ImSota/ZaruBall_casedata/case/Right/bottom_noMack.stl

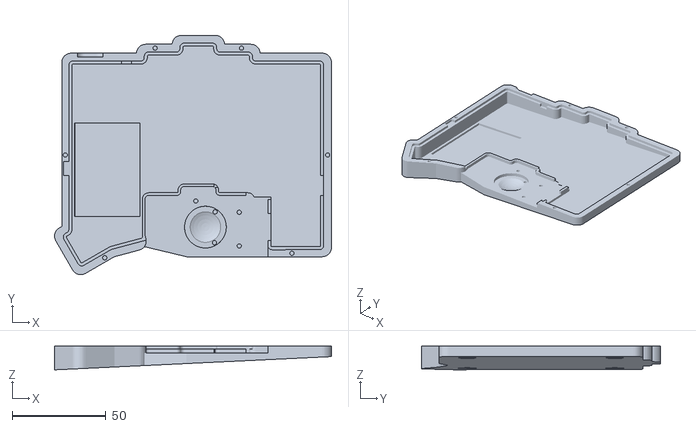
[picture p24: CAD file, 2025-06-08]
case/Right/bottom_noMack.stl
148.0 x 127.9 x 12.7
