ImSota/ZaruBall_casedata/case/Left/top_NP.stl

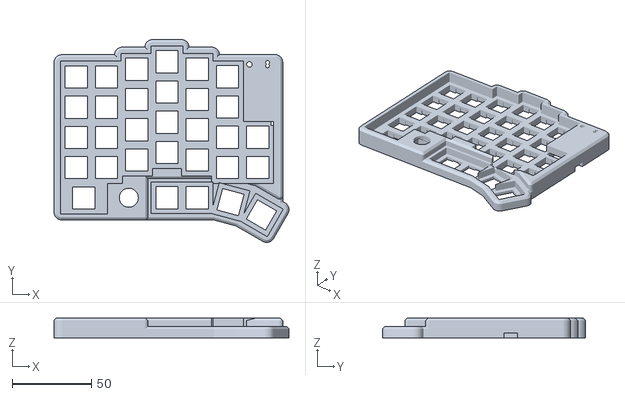
[picture p25: CAD file, 2025-06-08]
case/Left/top_NP.stl
148.0 x 127.8 x 12.5
