ImSota/ZaruBall_casedata/case/Right/top_LP.stl

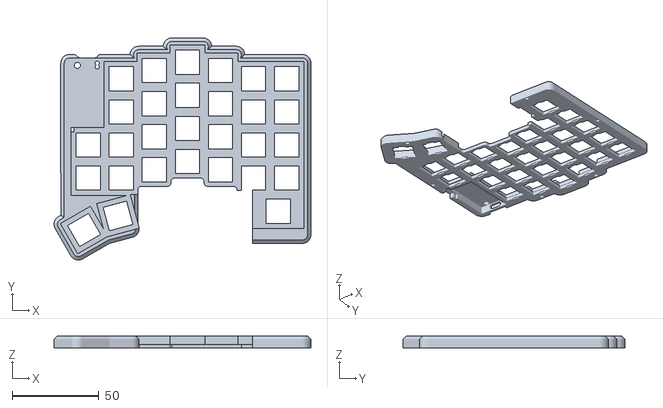
[picture p26: CAD file, 2025-06-08]
case/Right/top_LP.stl
148.0 x 127.9 x 7.20
